lbernache94/engineering-thesis-project/labview-interface/Picture3.png

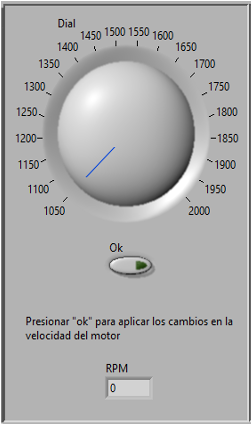
labview-interface/Picture3.png
