lbernache94/engineering-thesis-project/pcb-desing/arduino_shield_1.jpg

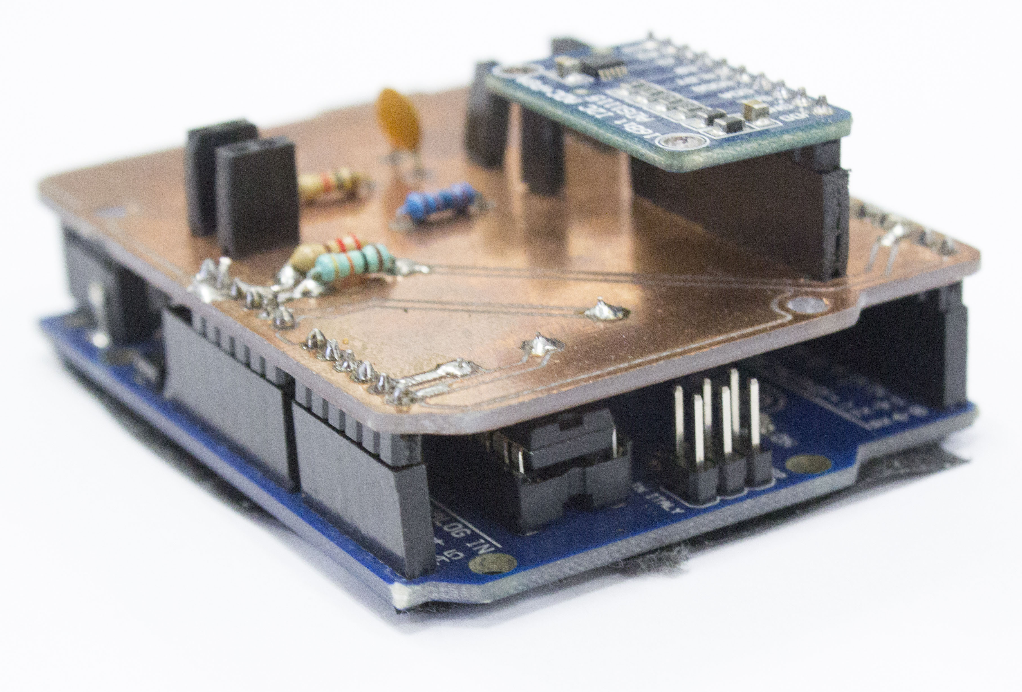
pcb-desing/arduino_shield_1.jpg
