lbernache94/engineering-thesis-project/mechanical-design/Ensamblaje completo.JPG

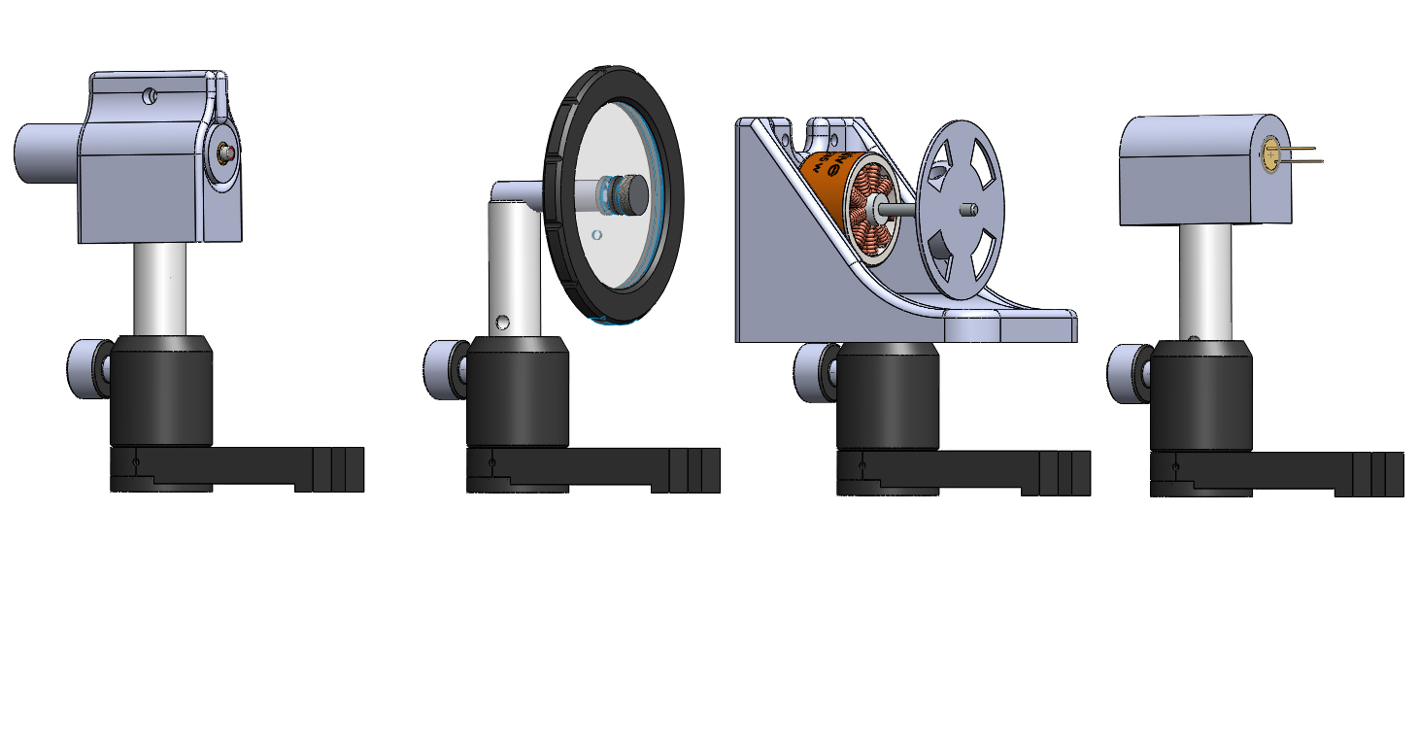
mechanical-design/Ensamblaje completo.JPG
