lbernache94/engineering-thesis-project/mechanical-design/Ensamblaje lateral.JPG

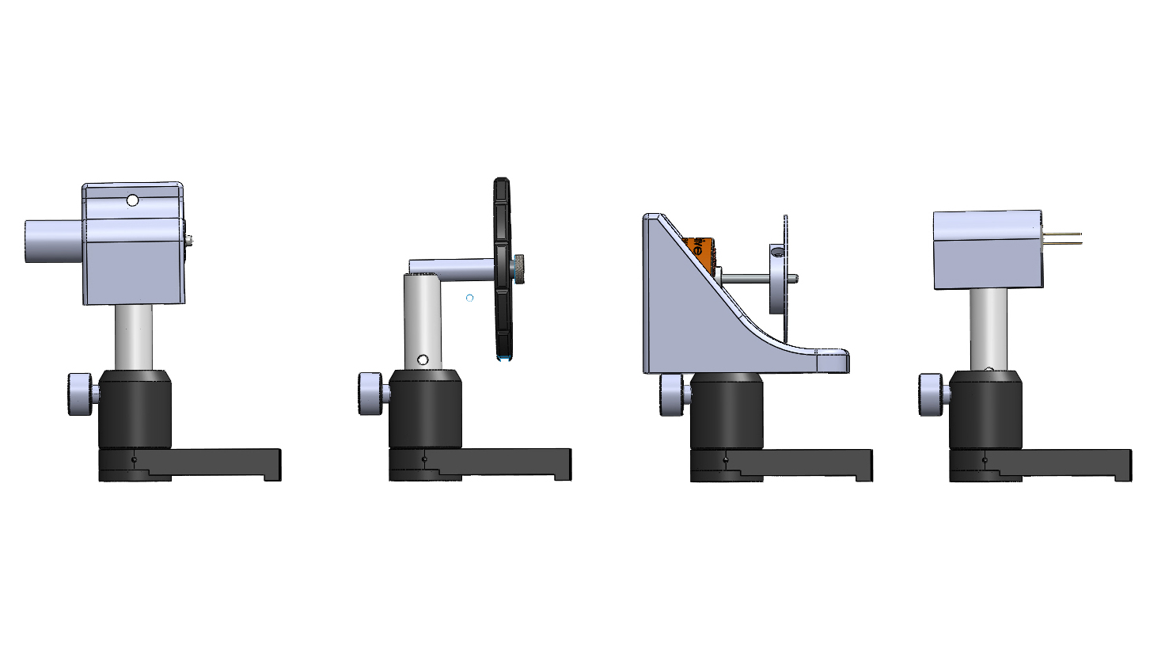
mechanical-design/Ensamblaje lateral.JPG
