lbernache94/engineering-thesis-project/mechanical-design/Ensamblaje vista aerea.JPG

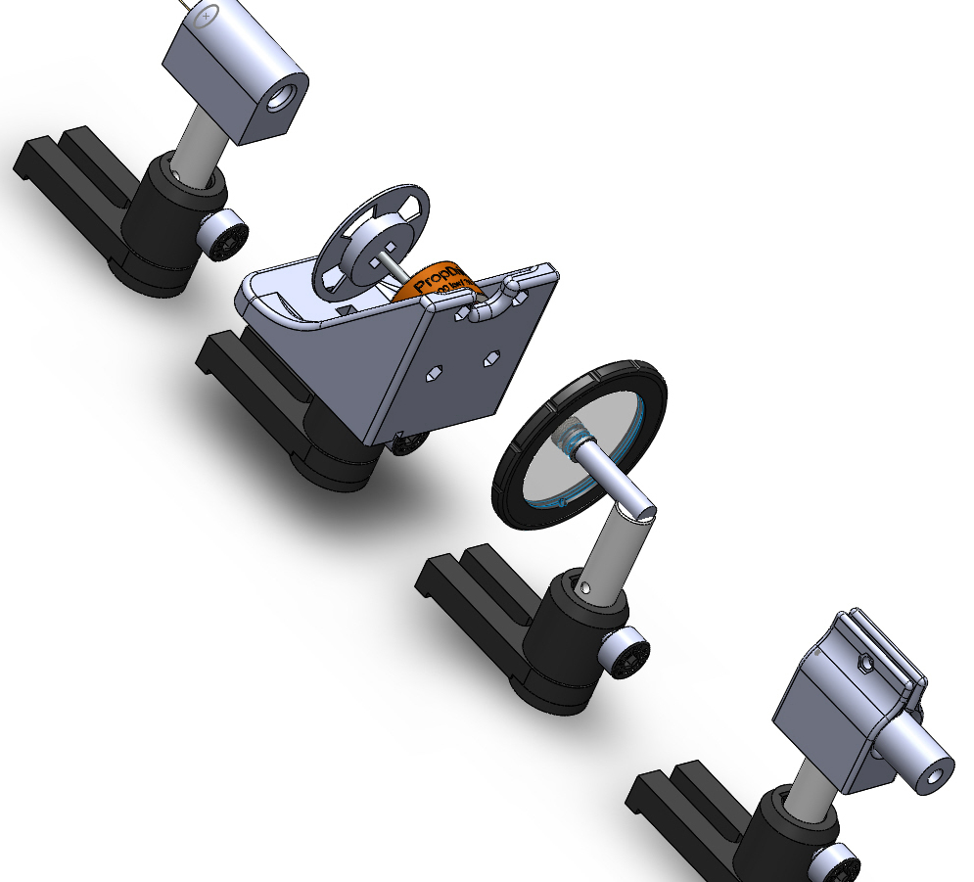
mechanical-design/Ensamblaje vista aerea.JPG
